hansgaensbauer/SimpleSBC/Hardware/Photos/X-Ray Report/1.jpg

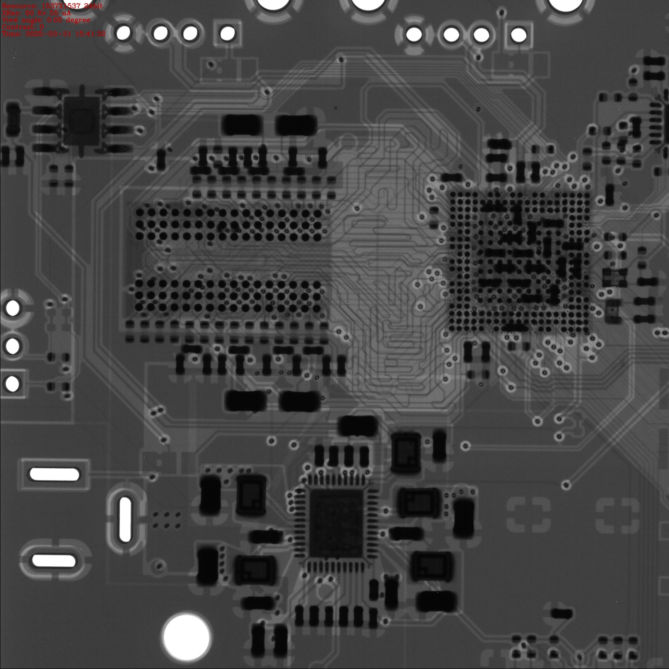
Hardware/Photos/X-Ray Report/1.jpg
