hansgaensbauer/SimpleSBC/Hardware/Photos/X-Ray Report/2.jpg

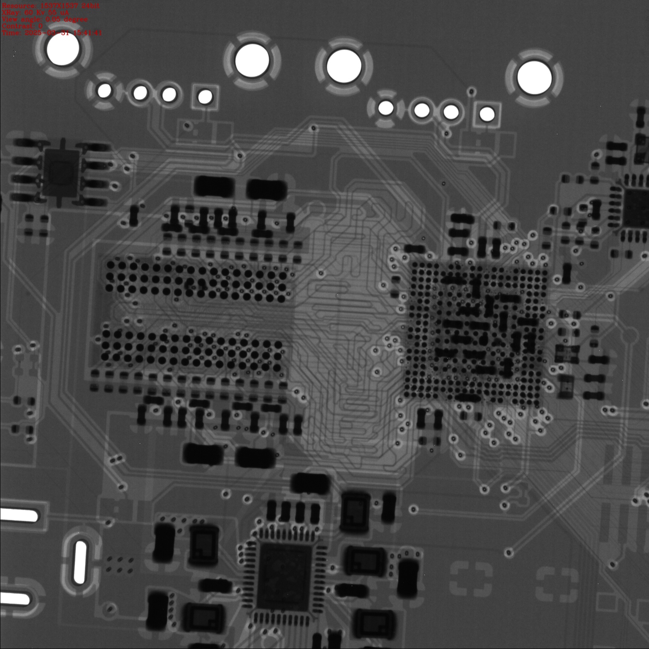
Hardware/Photos/X-Ray Report/2.jpg
